F6ITU/Alexiares_LPF/datasheet/Alex_TX.jpg

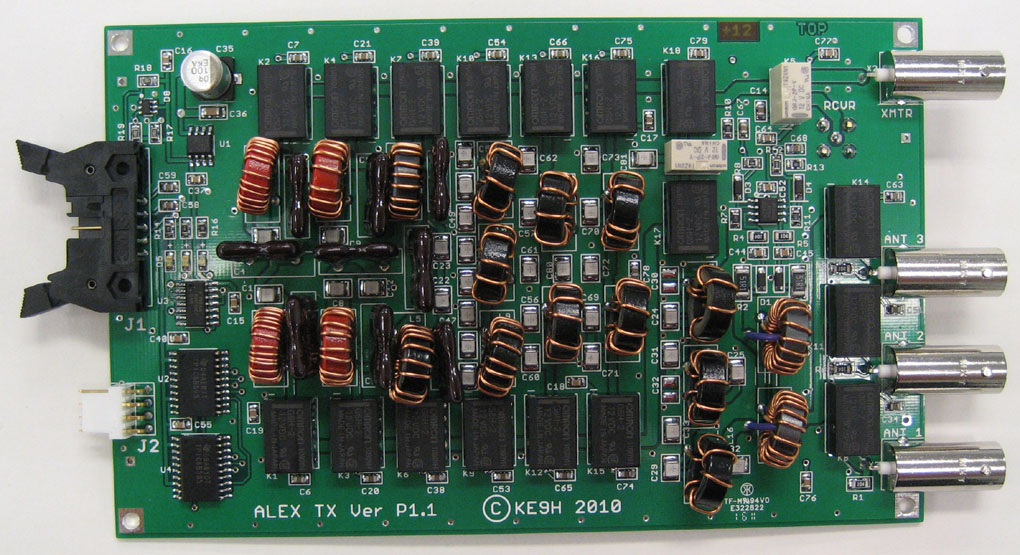
datasheet/Alex_TX.jpg
