F6ITU/Alexiares_LPF/images/dessous avec plan de masse.PNG

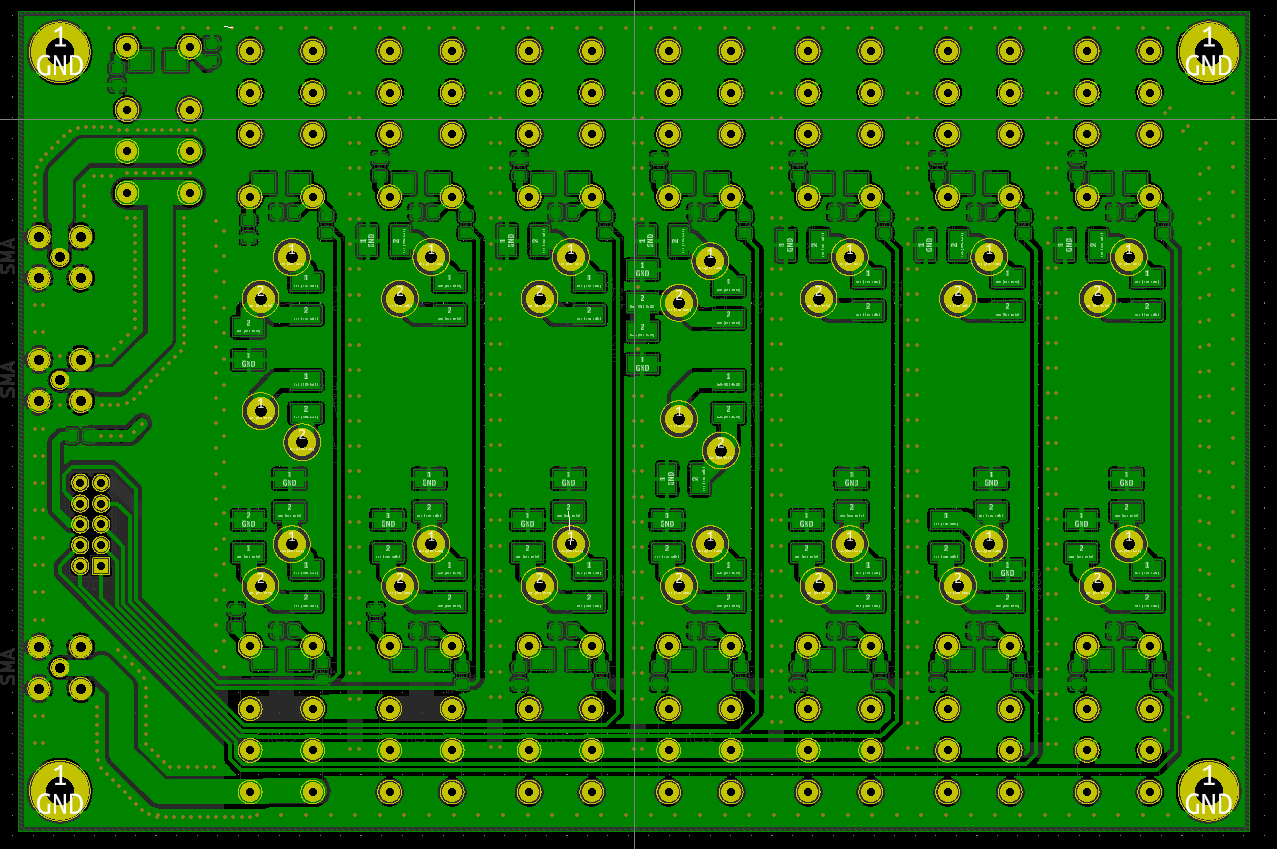
images/dessous avec plan de masse.PNG
