F6ITU/Alexiares_LPF/images/dessous pistes.PNG

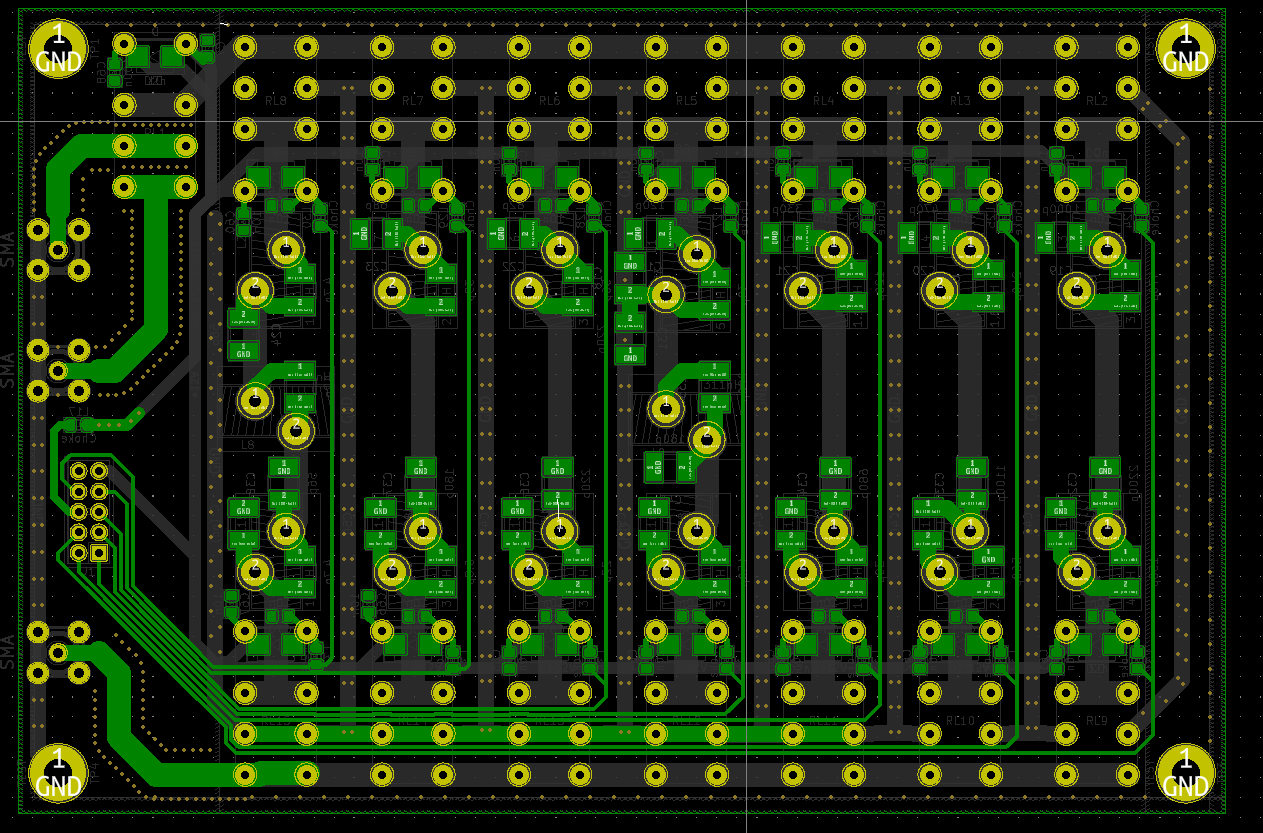
images/dessous pistes.PNG
