F6ITU/Alexiares_LPF/images/IMG_8971.JPG

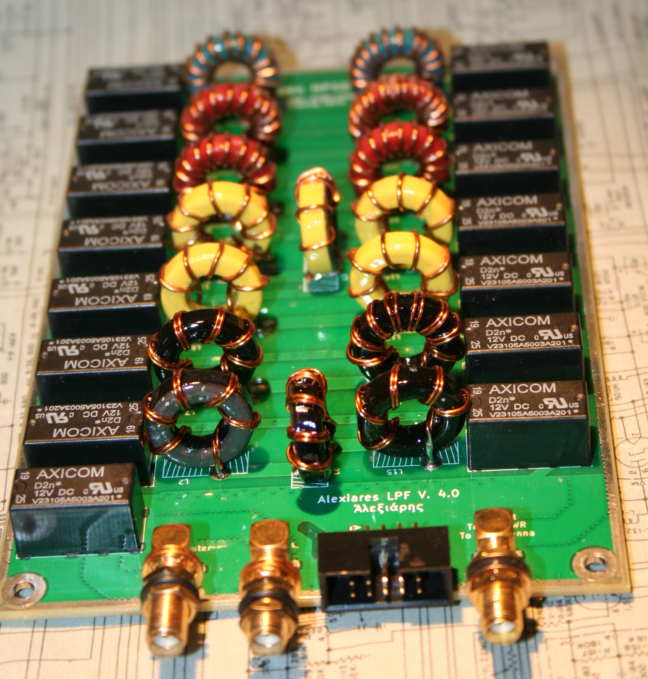
images/IMG_8971.JPG
