F6ITU/Alexiares_LPF/images/LPF V4.png

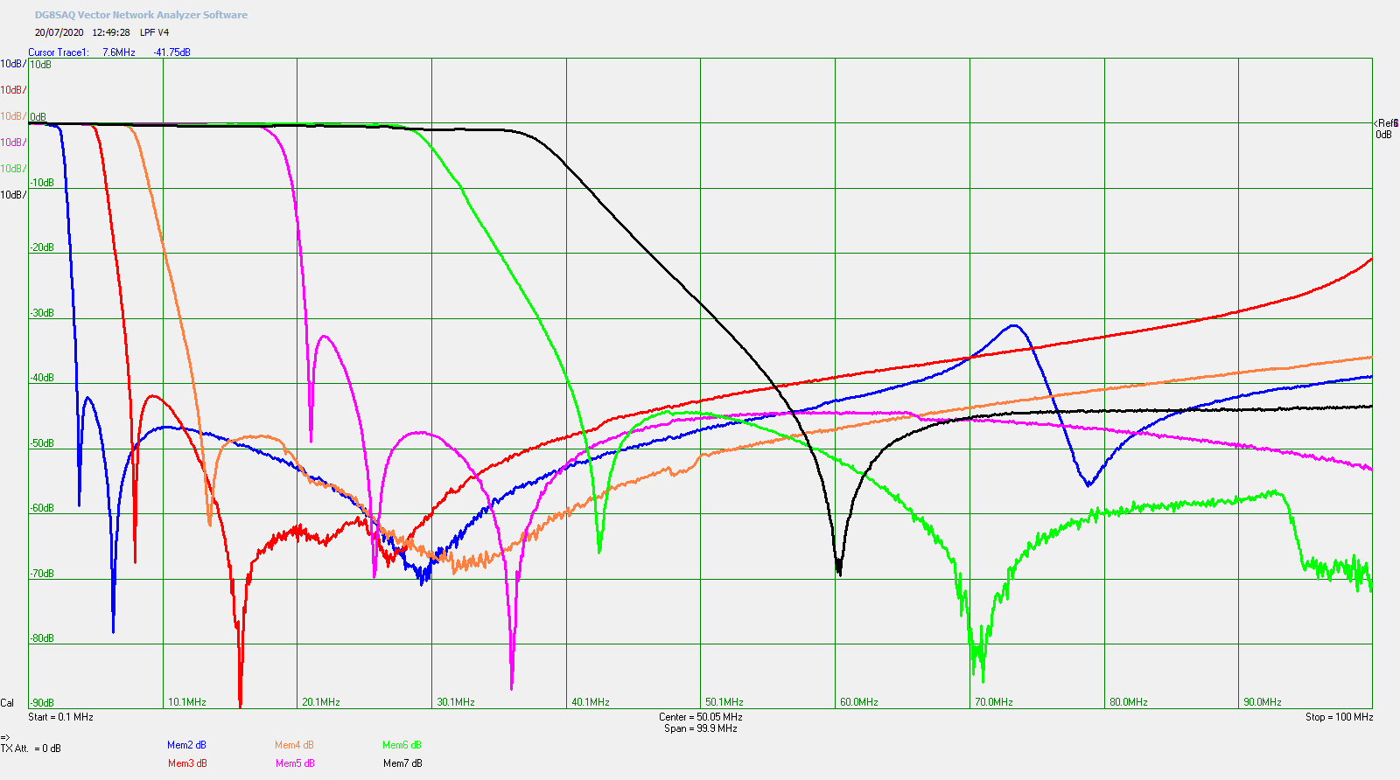
images/LPF V4.png
