F6ITU/Alexiares_LPF/images/LPF.png

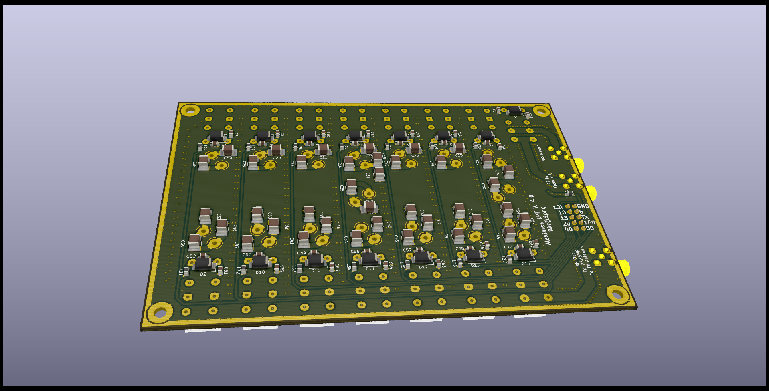
images/LPF.png
