F6ITU/Alexiares_LPF/Modules/params 2formC D2N THT.PNG

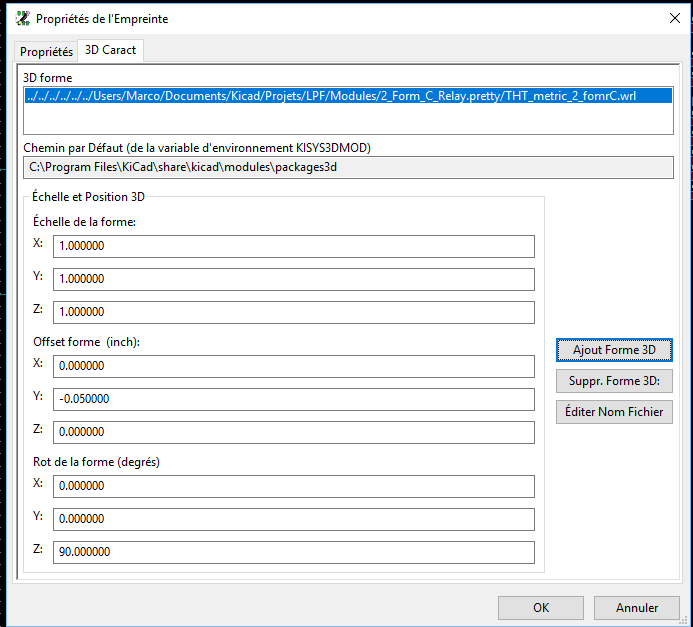
Modules/params 2formC D2N THT.PNG
